dbisk/chessexpress/src/board/game/game.h

/**
 * game.h
 * 
 * Declares functions for the "game" layer, which interfaces between the chess
 * constructs and the actual hardware control in order to induce movement on the
 * actual board.
 * 
 * @author Dean Biskup and Mitalee Bharadwaj
 * University of Illinois, ADSL (ECE 395), Fall 2019.
 */
#ifndef _GAME_GAME_H_
#define _GAME_GAME_H_

/**
 * gameLoop()
 * 
 * The entry point to the game.
 */
void gameLoop(void);

#endif // _GAME_GAME_H_
