dbisk/chessexpress/src/board/utils.h

/**
 * utils.h
 * 
 * Declares some useful functions
 * 
 * @author Dean Biskup and Mitalee Bharadwaj
 * University of Illinois, ADSL (ECE 395) Fall 2019
 */

#ifndef _UTILS_H_
#define _UTILS_H_

/**
 * abs(int)
 * 
 * Returns the absolute value of an integer.
 * 
 * @param x the integer 
 * @returns int the absolute value of x
 */
int abs(int x);

#endif // _UTILS_H_
